ArvoreDosSaberes/Embarcatech-Etapa-2---Projeto-Final/docs/aiot-tool-calling-embarcados/slides/17-conclusao.md

# 🎯 Conclusões e Próximos Passos

## O Que Aprendemos

- **IA é estatística avançada** — Não magia, mas muito útil
- **LLMs + Tool Calling** — Permitem decisões semânticas
- **AIoT** — ESP32 pode ser "inteligente" via nuvem
- **Granite TTM** — Séries temporais com fallback robusto
- **HTTPS no ESP32** — Viável e necessário

## Desafios para Explorar

- **Edge AI** — TinyML, TensorFlow Lite no ESP32
- **Latência** — Decisões locais vs. nuvem
- **Custo** — APIs pagas vs. modelos locais (Ollama)
- **Segurança** — Proteção de tokens e dados

## Recursos

- **Projeto Rack Inteligente**: github.com/...
- **Granite TTM**: ibm.github.io/granite-tsfm
- **ESP-IDF**: docs.espressif.com
- **Ollama**: ollama.ai

> "O melhor momento para começar com IA embarcada foi ontem. O segundo melhor é agora!"
