ArvoreDosSaberes/Embarcatech-Etapa-2---Projeto-Final/docs/aiot-tool-calling-embarcados/slides/index.md

---
title: "AIoT e Tool Calling em Sistemas Embarcados"
subtitle: "Da IA na Nuvem ao ESP32"
authors:
  - "Carlos Delfino Carvalho Pinheiro"
date: "2025"
description: "Apresentação para a comunidade Embarcados sobre AIoT, Tool Calling e integração de LLMs com microcontroladores"
tags:
  - "AIoT"
  - "Tool Calling"
  - "ESP32"
  - "LLM"
  - "Sistemas Embarcados"
---
