ArvoreDosSaberes/Embarcatech-Etapa-2---Projeto-Final/docs/aiot-tool-calling-embarcados/slides/03-ia-vs-ai.md

# 🤔 "Inteligência Artificial" — É Certo Usar Este Nome?

## O Debate Histórico

- **1956**: John McCarthy cunhou o termo "Artificial Intelligence"
- O termo foi **marketing** para obter financiamento de pesquisa
- Críticos argumentam: máquinas não "pensam", apenas **processam padrões**

## O Que Realmente Temos Hoje

| O que chamamos | O que realmente é |
|---|---|
| IA | Estatística avançada + Álgebra linear |
| Aprendizado | Otimização de parâmetros |
| Inteligência | Reconhecimento de padrões |
| Compreensão | Correlação probabilística |

## Por Que Usamos Mesmo Assim?

- **Convenção** — O termo está consolidado
- **Comunicação** — Facilita o diálogo com não-técnicos
- **Evolução** — O significado acompanha a tecnologia

> "Toda tecnologia suficientemente avançada é indistinguível de magia" — Arthur C. Clarke
