ArvoreDosSaberes/Embarcatech-Etapa-2---Projeto-Final/docs/aiot-tool-calling-embarcados/slides/04-genai-llm.md

# 🧠 GenAIs e LLMs — O Que São?

## Generative AI (GenAI)

Sistemas capazes de **gerar conteúdo novo**:
- Texto, imagens, código, áudio, vídeo
- Baseados em padrões aprendidos de dados massivos

## Large Language Models (LLMs)

Modelos de linguagem com **bilhões de parâmetros**:
- **GPT** (OpenAI) — 175B+ parâmetros
- **Granite** (IBM) — Modelos especializados
- **Llama** (Meta) — Open source
- **Gemini** (Google) — Multimodal

## Como Funcionam?

```
[Texto de Entrada] → [Tokenização] → [Embedding] 
         ↓
    [Transformer]
         ↓
[Predição do Próximo Token] → [Decodificação] → [Resposta]
```

## Limitações Importantes

- **Não "entendem"** — Apenas correlacionam padrões
- **Alucinações** — Podem inventar informações
- **Custo computacional** — Exigem muita memória/processamento
