ArvoreDosSaberes/Embarcatech-Etapa-2---Projeto-Final/docs/aiot-tool-calling-embarcados/slides/18-obrigado.md

# 🙏 Obrigado!

## Contato

**Carlos Delfino Carvalho Pinheiro**

- 🧔 Membro honorário da Beard Brotherhood
- 💼 Desenvolvedor Embarcado & IoT
- 🎓 EmbarcaTech TIC-27

---

## Perguntas?

> "A única pergunta boba é aquela que não foi feita!"

---

## Links Úteis

- **OpenAI Docs**: platform.openai.com/docs
- **ESP-IDF HTTPS**: docs.espressif.com/projects/esp-idf
- **IBM Granite**: github.com/ibm-granite
- **Comunidade Embarcados**: embarcados.com.br
