ArvoreDosSaberes/Embarcatech-Etapa-2---Projeto-Final/docs/esquemático/Esquemático Final/3D/3D_1/WhatsApp Image 2024-02-20 at 16.13.23.jpeg

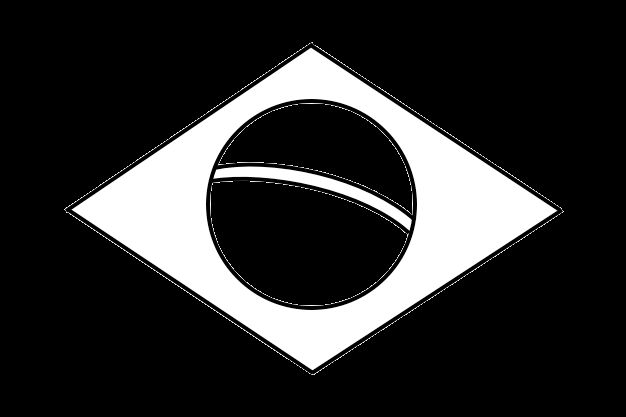
docs/esquemático/Esquemático Final/3D/3D_1/WhatsApp Image 2024-02-20 at 16.13.23.jpeg
