ArvoreDosSaberes/Embarcatech-Etapa-2---Projeto-Final/docs/esquemático/Esquemático Final/3D/3D_1/SMT-microinterruptor moment neo.SLDPRT

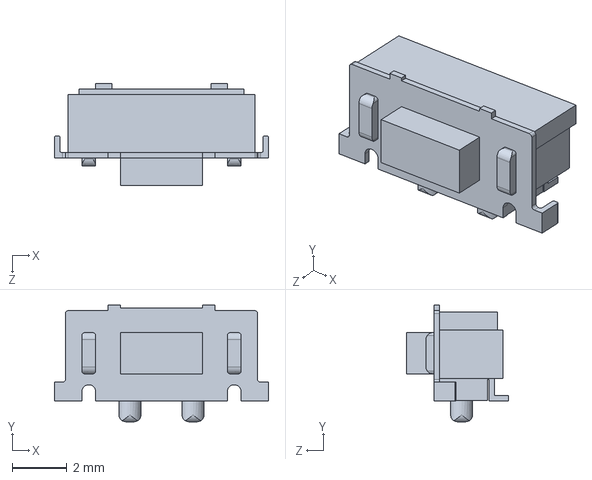
[picture p29: CAD file, 2026-01-02]
docs/esquemático/Esquemático Final/3D/3D_1/SMT-microinterruptor moment neo.SLDPRT
7.80 x 4.25 x 3.70 mm
