ArvoreDosSaberes/Embarcatech-Etapa-2---Projeto-Final/docs/esquemático/Esquemático Final/3D/DS1021_blue_2x01p_100mil_Type5_rev1.0.STEP

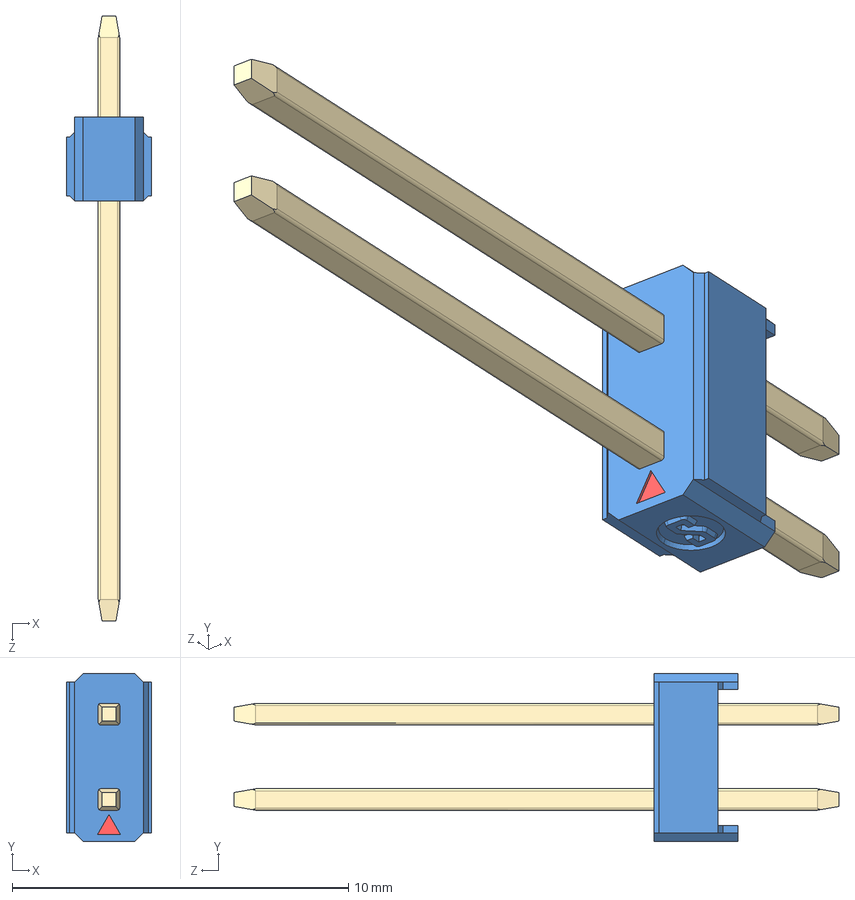
[picture p30: CAD file, 2026-01-02]
docs/esquemático/Esquemático Final/3D/DS1021_blue_2x01p_100mil_Type5_rev1.0.STEP
2.54 x 5.00 x 18.0 mm
