ArvoreDosSaberes/Embarcatech-Etapa-2---Projeto-Final/docs/esquemático/Esquemático Final/3D/3D_1/LED SMD 5050 RGB.stp

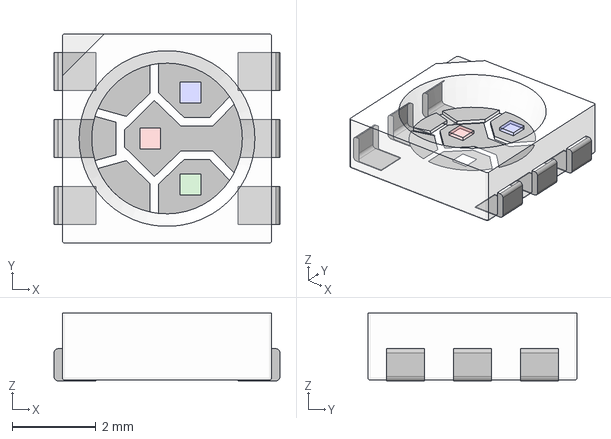
[picture p31: CAD file, 2026-01-02]
docs/esquemático/Esquemático Final/3D/3D_1/LED SMD 5050 RGB.stp
5.40 x 5.00 x 1.62 mm
