ArvoreDosSaberes/Embarcatech-Etapa-2---Projeto-Final/docs/esquemático/Esquemático Final/3D/CONB127P-2R-14W_TH.STEP

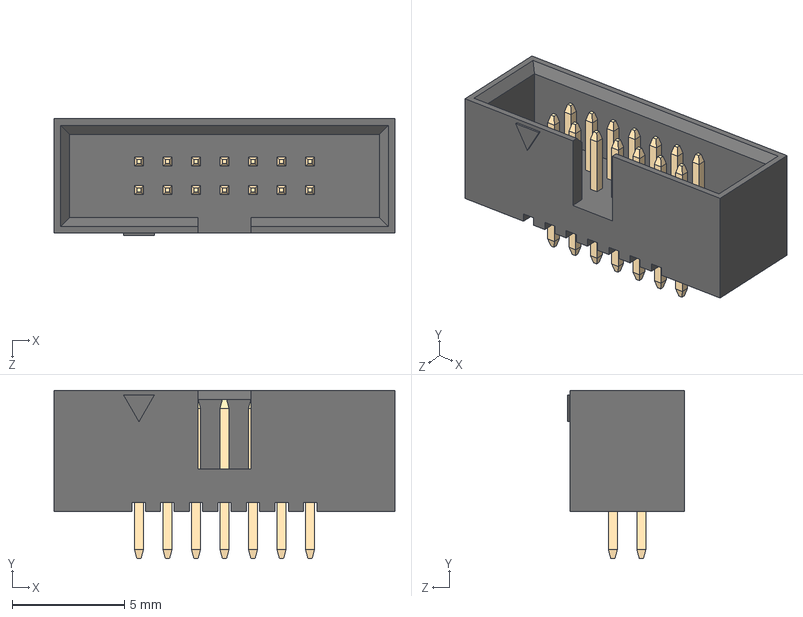
[picture p32: CAD file, 2026-01-02]
docs/esquemático/Esquemático Final/3D/CONB127P-2R-14W_TH.STEP
15.2 x 7.50 x 5.20 mm
