ArvoreDosSaberes/Embarcatech-Etapa-2---Projeto-Final/docs/esquemático/Esquemático Final/3D/3D_1/SOP-8.STEP

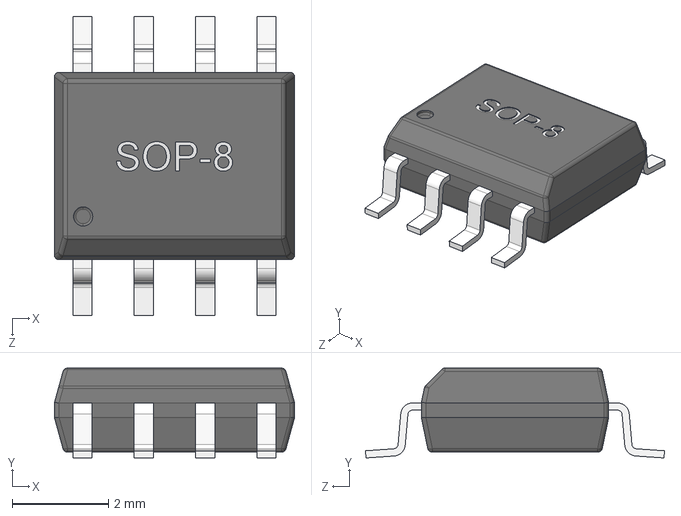
[picture p33: CAD file, 2026-01-02]
docs/esquemático/Esquemático Final/3D/3D_1/SOP-8.STEP
5.00 x 1.87 x 6.22 mm
