ArvoreDosSaberes/Embarcatech-Etapa-2---Projeto-Final/docs/esquemático/Esquemático Final/3D/TL800-02.STEP

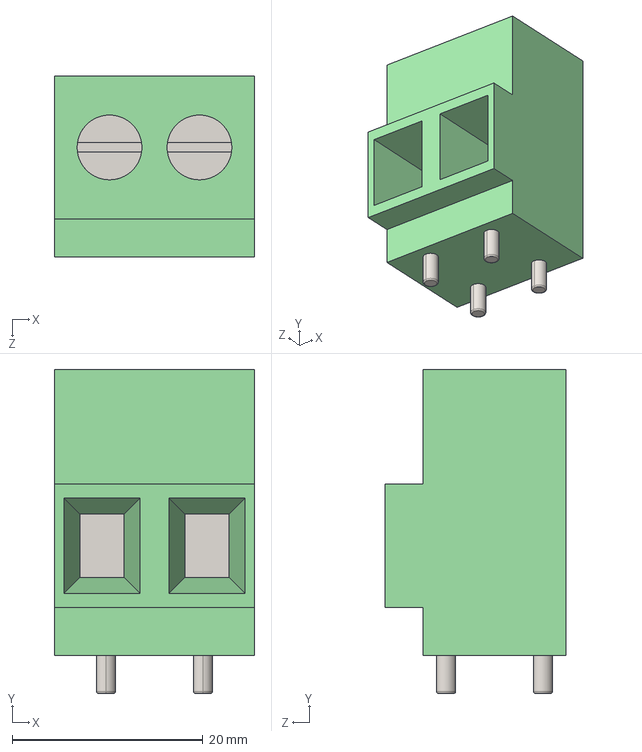
[picture p34: CAD file, 2026-01-02]
docs/esquemático/Esquemático Final/3D/TL800-02.STEP
21.0 x 34.0 x 19.0 mm
