ArvoreDosSaberes/Embarcatech-Etapa-2---Projeto-Final/docs/esquemático/Esquemático Final/3D/12mm Push Button with Cap.STEP

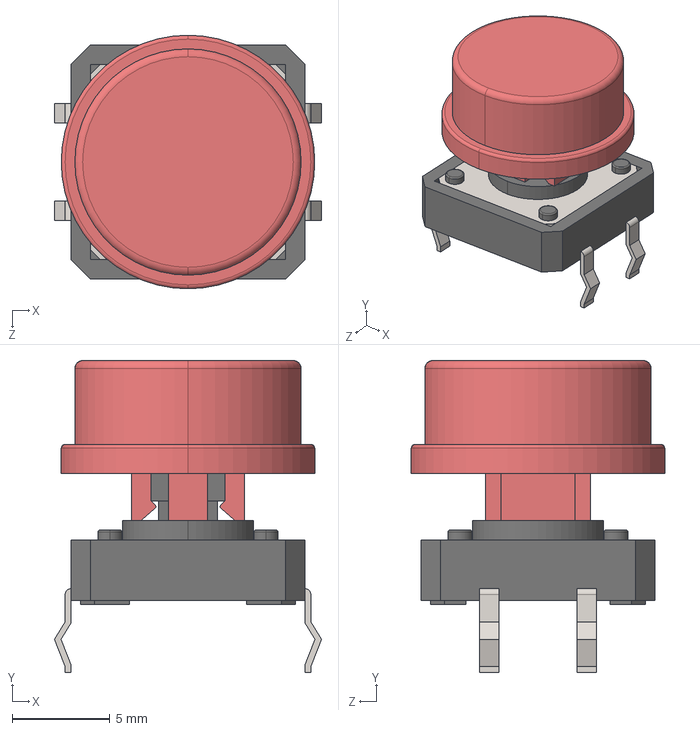
[picture p35: CAD file, 2026-01-02]
docs/esquemático/Esquemático Final/3D/12mm Push Button with Cap.STEP
13.7 x 16.0 x 13.0 mm
12mm Push Button
12mm Push Button Cap
