ArvoreDosSaberes/Embarcatech-Etapa-2---Projeto-Final/docs/esquemático/Esquemático Final/3D/3D_1/SC70-5.step

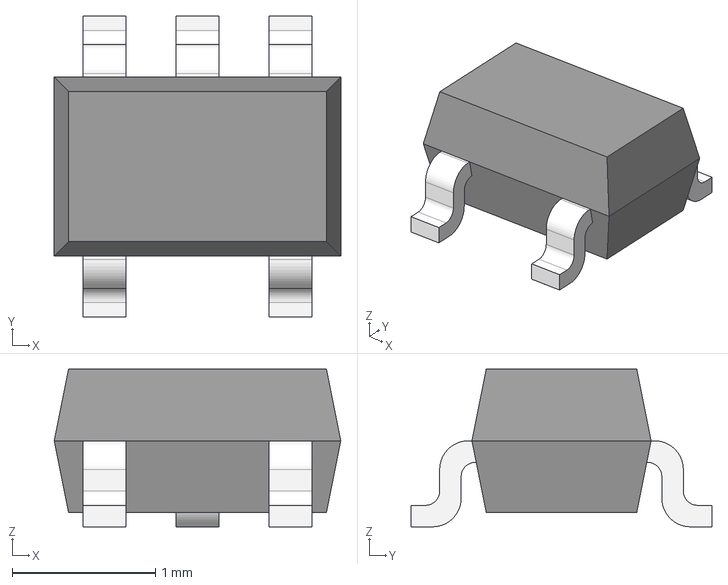
[picture p36: CAD file, 2026-01-02]
docs/esquemático/Esquemático Final/3D/3D_1/SC70-5.step
2.00 x 2.10 x 1.10 mm
