ArvoreDosSaberes/Embarcatech-Etapa-2---Projeto-Final/docs/esquemático/Esquemático Final/3D/3D_1/PLS-1X5.step

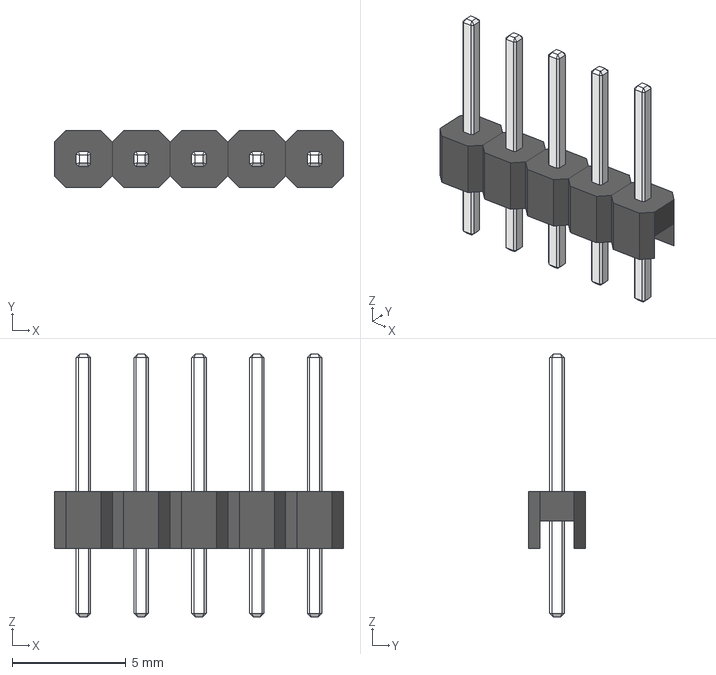
[picture p37: CAD file, 2026-01-02]
docs/esquemático/Esquemático Final/3D/3D_1/PLS-1X5.step
12.7 x 2.50 x 11.5 mm
