ArvoreDosSaberes/Embarcatech-Etapa-2---Projeto-Final/docs/esquemático/Esquemático Final/3D/LED - SMD RGB (WS2812).sldprt

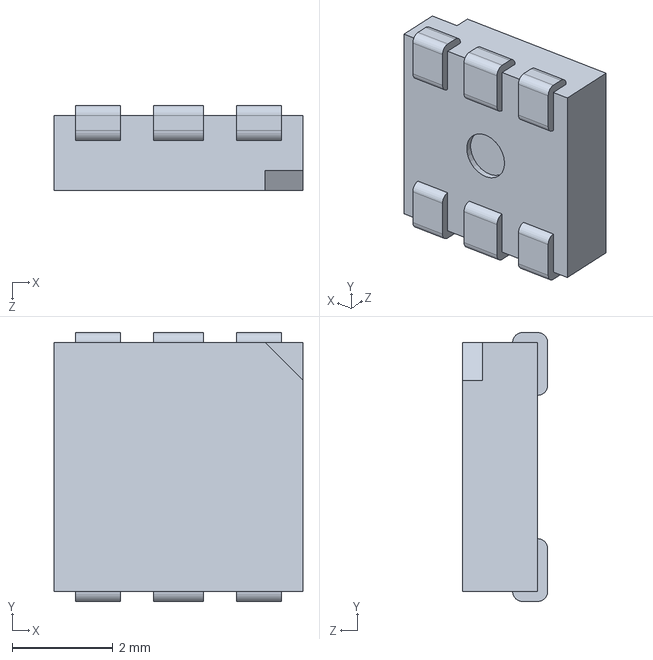
[picture p38: CAD file, 2026-01-02]
docs/esquemático/Esquemático Final/3D/LED - SMD RGB (WS2812).sldprt
4.95 x 5.35 x 1.70 mm
