ArvoreDosSaberes/Embarcatech-Etapa-2---Projeto-Final/docs/esquemático/Esquemático Final/3D/3D_1/SOT-23.step

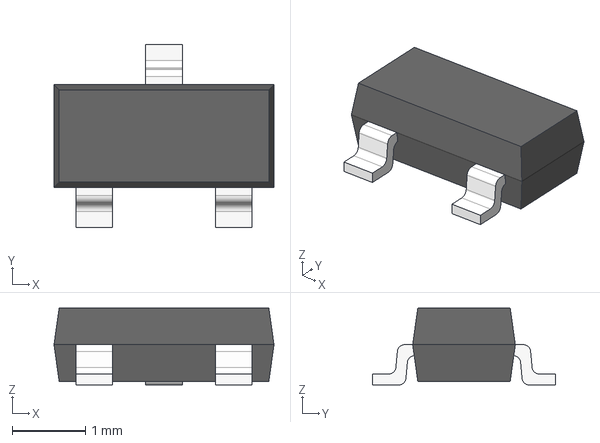
[picture p39: CAD file, 2026-01-02]
docs/esquemático/Esquemático Final/3D/3D_1/SOT-23.step
3.00 x 2.50 x 1.05 mm
