ArvoreDosSaberes/Embarcatech-Etapa-2---Projeto-Final/docs/esquemático/Esquemático Final/3D/3D_1/HwIT-Without-Slogan-800x600.dxf

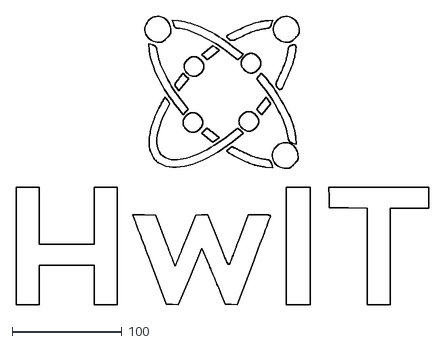
[picture p40: CAD file, 2026-01-02]
docs/esquemático/Esquemático Final/3D/3D_1/HwIT-Without-Slogan-800x600.dxf
376.0 x 262.9
