ArvoreDosSaberes/Embarcatech-Etapa-2---Projeto-Final/docs/esquemático/Esquemático Final/3D/C_0805.STEP

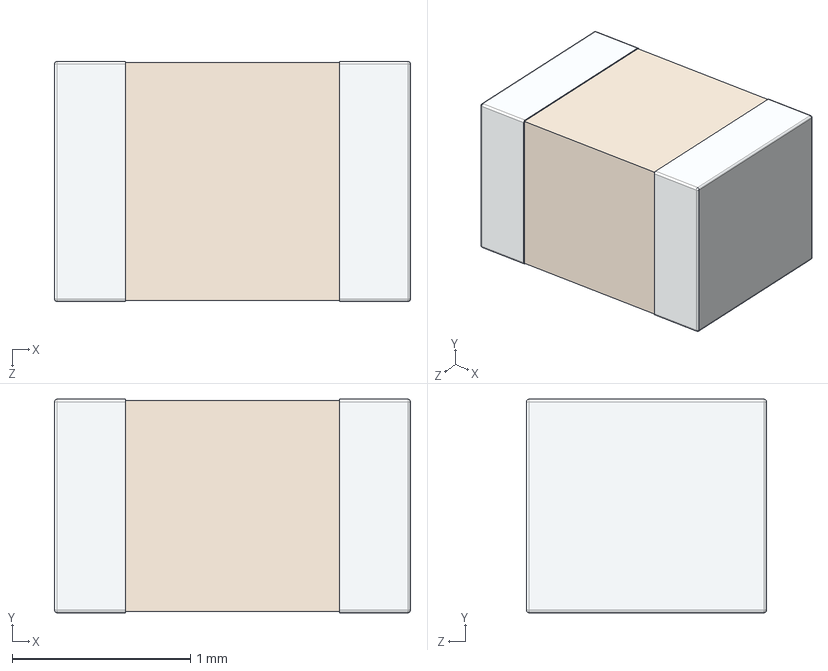
[picture p41: CAD file, 2026-01-02]
docs/esquemático/Esquemático Final/3D/C_0805.STEP
2.00 x 1.20 x 1.35 mm
