ArvoreDosSaberes/Embarcatech-Etapa-2---Projeto-Final/docs/esquemático/Esquemático Final/3D/3D_1/AB2_HDR_M07-2V-S-TE_WINGS3D.stl

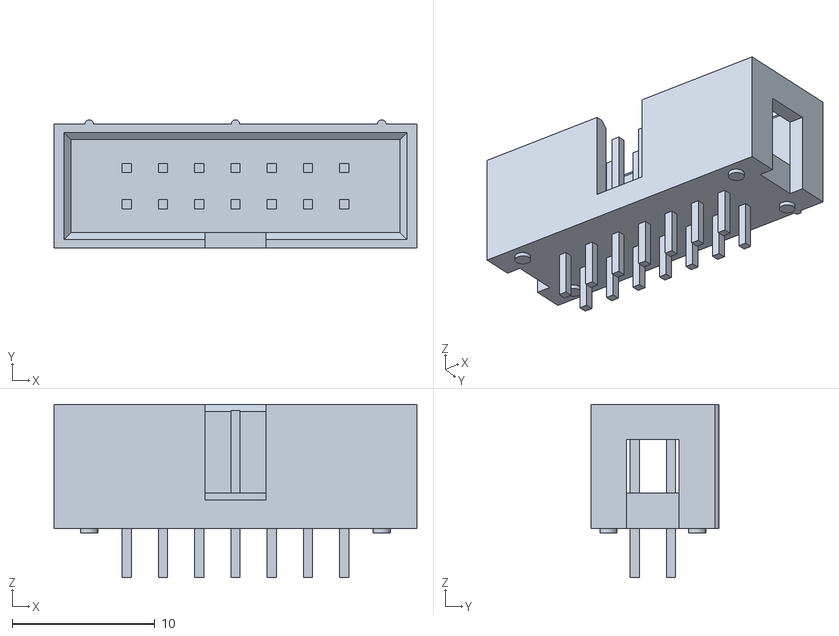
[picture p42: CAD file, 2026-01-02]
docs/esquemático/Esquemático Final/3D/3D_1/AB2_HDR_M07-2V-S-TE_WINGS3D.stl
25.4 x 9.00 x 12.1
