ArvoreDosSaberes/Embarcatech-Etapa-2---Projeto-Final/docs/esquemático/Esquemático Final/3D/Resistor_0603_Ohm.step

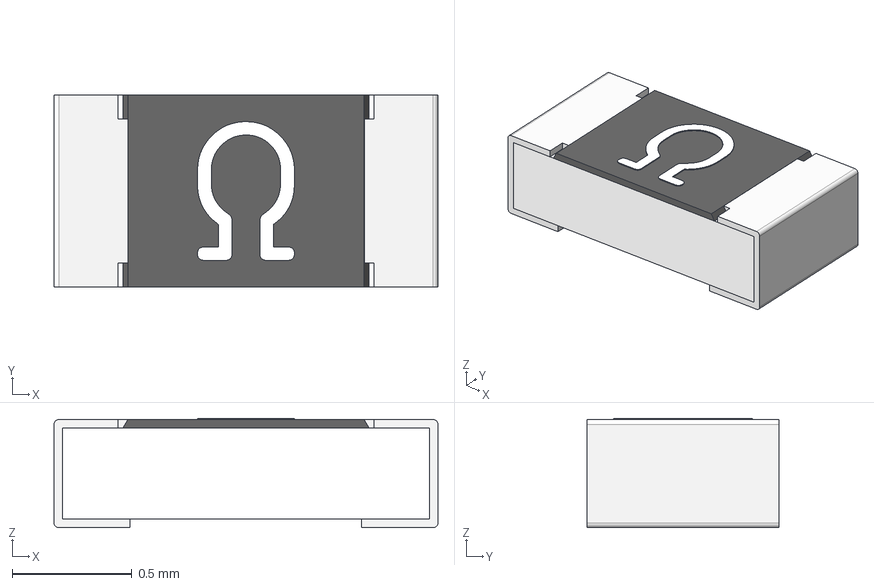
[picture p43: CAD file, 2026-01-02]
docs/esquemático/Esquemático Final/3D/Resistor_0603_Ohm.step
1.60 x 0.8 x 0.455 mm
Pin1Body
Pin2Body
CeramicBody
CoatingBody
TextBody
