ArvoreDosSaberes/Embarcatech-Etapa-2---Projeto-Final/docs/esquemático/Esquemático Final/3D/3D_1/EVM-3E.STEP

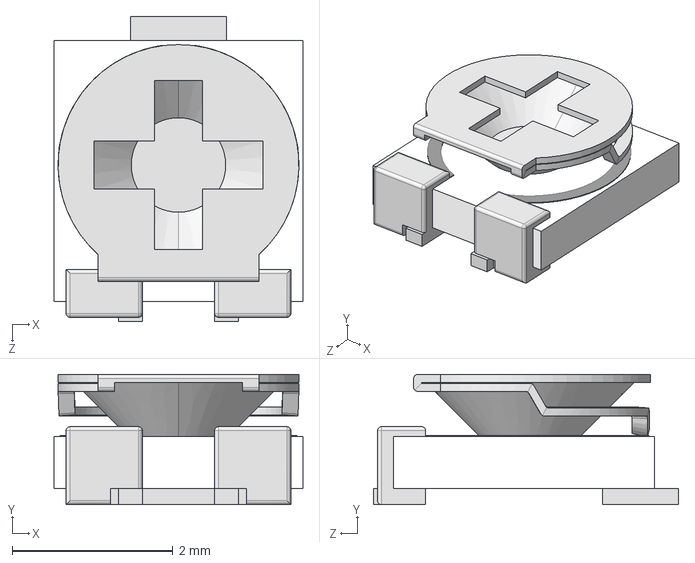
[picture p44: CAD file, 2026-01-02]
docs/esquemático/Esquemático Final/3D/3D_1/EVM-3E.STEP
3.10 x 1.62 x 3.80 mm
