ArvoreDosSaberes/Embarcatech-Etapa-2---Projeto-Final/docs/esquemático/Esquemático Final/3D/3D_1/C_0603.STEP

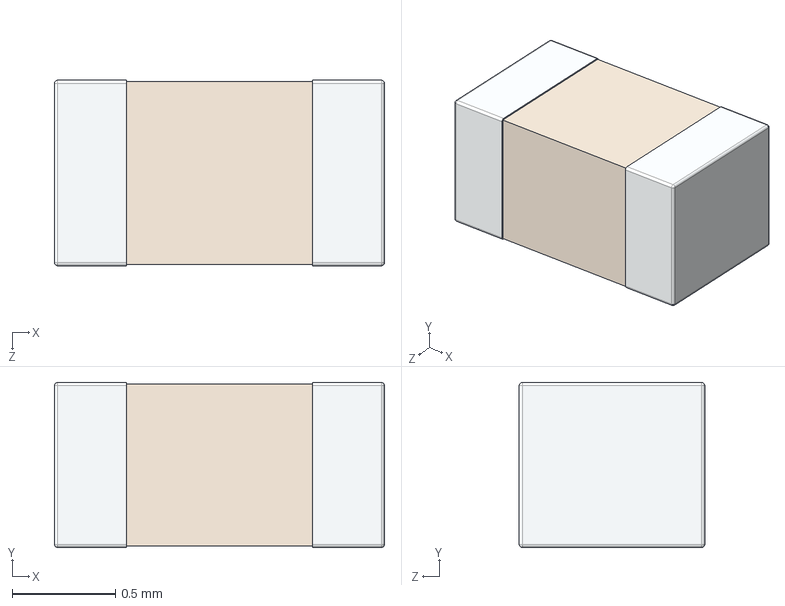
[picture p45: CAD file, 2026-01-02]
docs/esquemático/Esquemático Final/3D/3D_1/C_0603.STEP
1.60 x 0.8 x 0.9 mm
