ArvoreDosSaberes/Embarcatech-Etapa-2---Projeto-Final/docs/esquemático/Esquemático Final/3D/smd Led 5050 v3.step

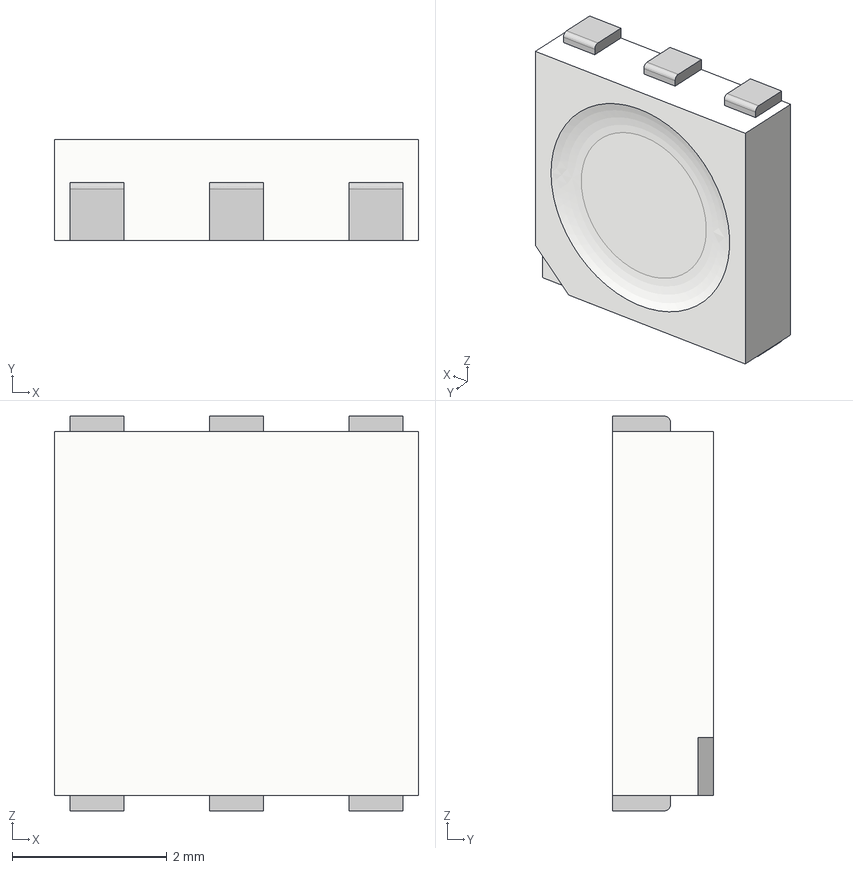
[picture p46: CAD file, 2026-01-02]
docs/esquemático/Esquemático Final/3D/smd Led 5050 v3.step
4.70 x 1.30 x 5.10 mm
