ArvoreDosSaberes/Embarcatech-Etapa-2---Projeto-Final/docs/esquemático/Esquemático Final/3D/3D_1/pin header pitch v4.step

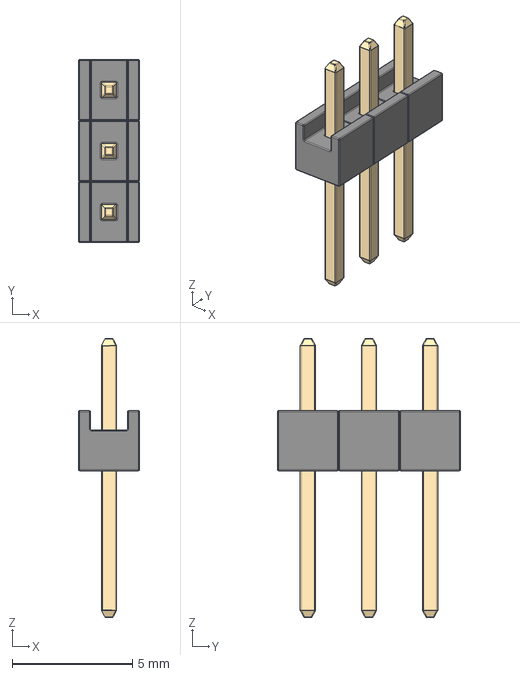
[picture p47: CAD file, 2026-01-02]
docs/esquemático/Esquemático Final/3D/3D_1/pin header pitch v4.step
2.54 x 7.62 x 11.6 mm
