ArvoreDosSaberes/Embarcatech-Etapa-2---Projeto-Final/docs/esquemático/Esquemático Final/3D/JST XH 4 B4B-XH-A.STEP

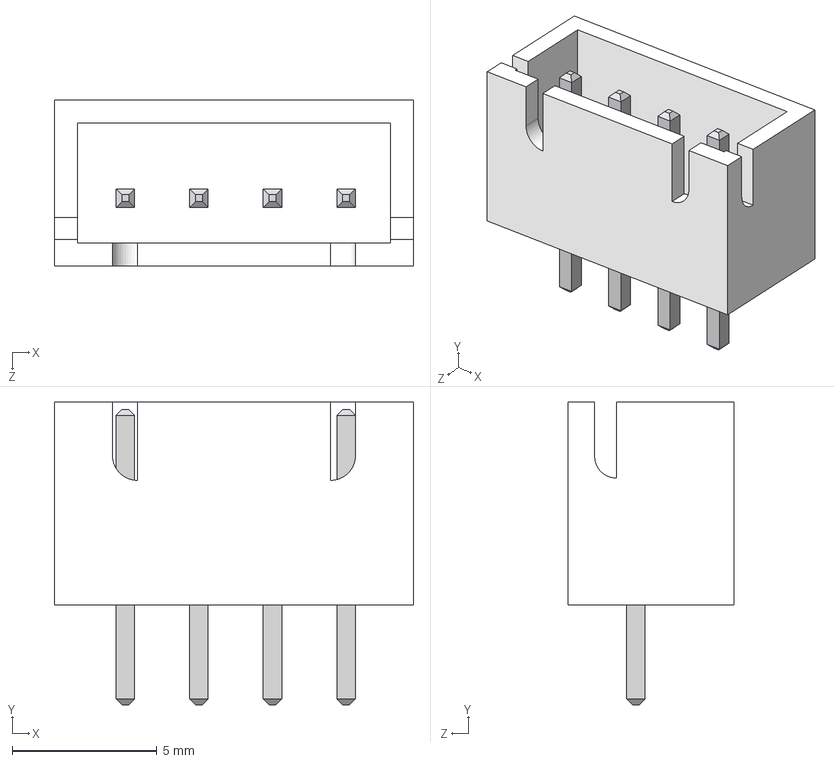
[picture p48: CAD file, 2026-01-02]
docs/esquemático/Esquemático Final/3D/JST XH 4 B4B-XH-A.STEP
12.4 x 10.5 x 5.75 mm
