ArvoreDosSaberes/Embarcatech-Etapa-2---Projeto-Final/docs/esquemático/Esquemático Final/3D/Pushbutton (TC-1101DE-B-D_C561494) Code _ B.step

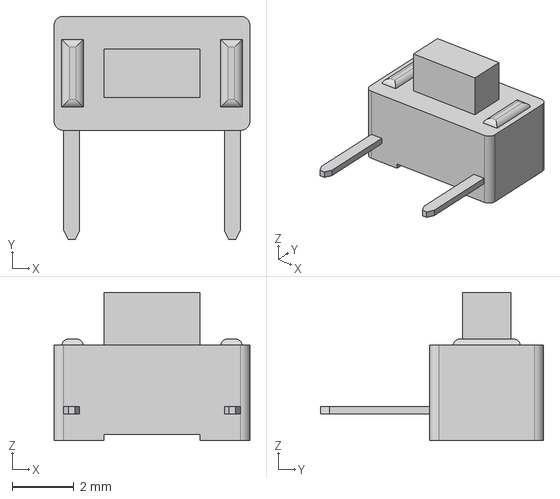
[picture p49: CAD file, 2026-01-02]
docs/esquemático/Esquemático Final/3D/Pushbutton (TC-1101DE-B-D_C561494) Code _ B.step
6.34 x 7.23 x 4.80 mm
