ArvoreDosSaberes/Embarcatech-Etapa-2---Projeto-Final/docs/esquemático/Esquemático Final/3D/C_0402.STEP

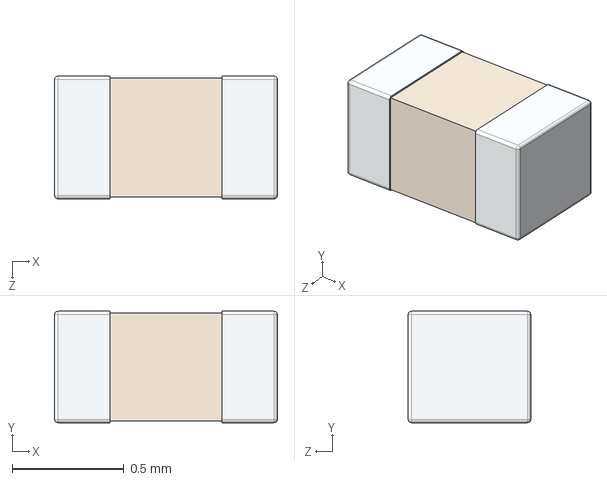
[picture p50: CAD file, 2026-01-02]
docs/esquemático/Esquemático Final/3D/C_0402.STEP
1.00 x 0.5 x 0.55 mm
