ArvoreDosSaberes/Embarcatech-Etapa-2---Projeto-Final/docs/esquemático/Esquemático Final/3D/3D_1/AnyConv.com__HwIT Without Slogan 2400x1800.dxf

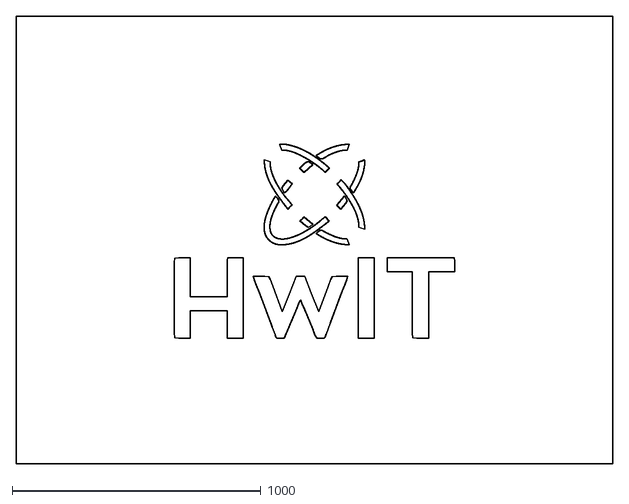
[picture p51: CAD file, 2026-01-02]
docs/esquemático/Esquemático Final/3D/3D_1/AnyConv.com__HwIT Without Slogan 2400x1800.dxf
2400.0 x 1800.0
