ArvoreDosSaberes/Embarcatech-Etapa-2---Projeto-Final/docs/esquemático/Esquemático Final/3D/MAX4466 Mic Amp.STEP

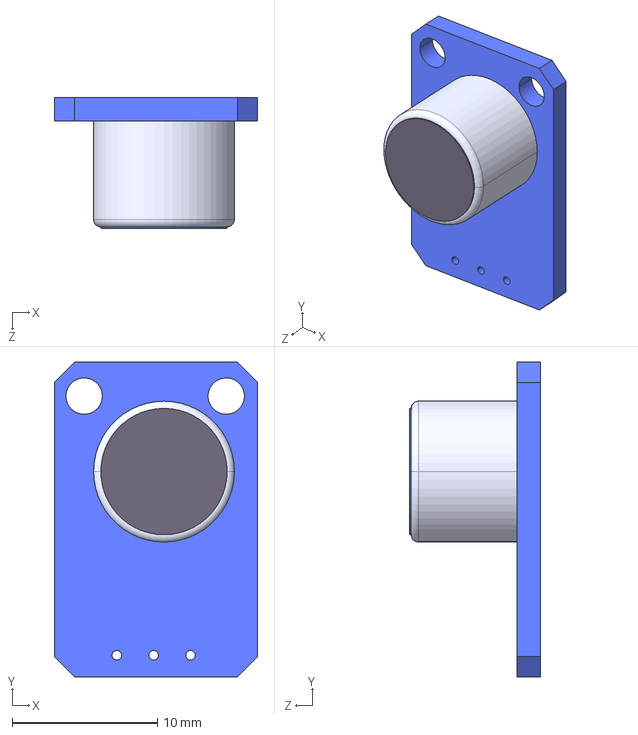
[picture p52: CAD file, 2026-01-02]
docs/esquemático/Esquemático Final/3D/MAX4466 Mic Amp.STEP
14.0 x 21.7 x 9.00 mm
