ArvoreDosSaberes/Embarcatech-Etapa-2---Projeto-Final/docs/esquemático/Esquemático Final/3D/3D_1/PSM8050 Series SMD Molding inductor.STEP

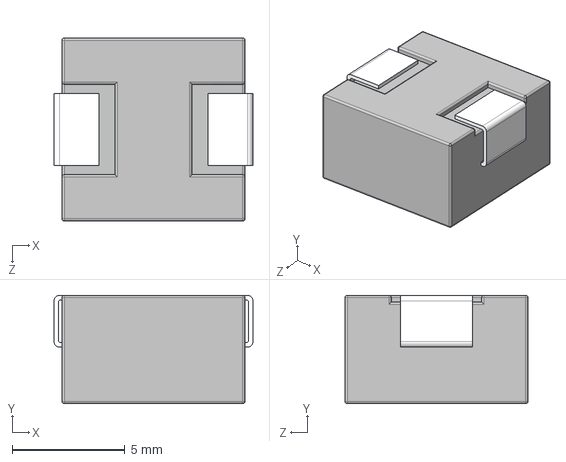
[picture p53: CAD file, 2026-01-02]
docs/esquemático/Esquemático Final/3D/3D_1/PSM8050 Series SMD Molding inductor.STEP
8.81 x 4.80 x 8.10 mm
