ArvoreDosSaberes/Embarcatech-Etapa-2---Projeto-Final/docs/esquemático/Esquemático Final/3D/SparkFun Deluxe Thumbstick with Breakout Board and Knob.step

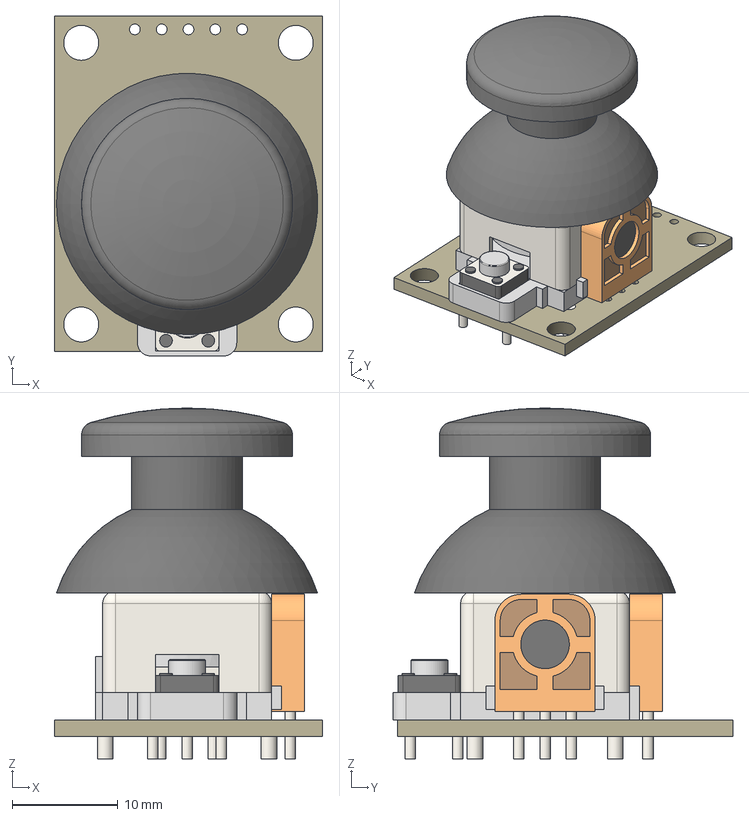
[picture p54: CAD file, 2026-01-02]
docs/esquemático/Esquemático Final/3D/SparkFun Deluxe Thumbstick with Breakout Board and Knob.step
25.4 x 32.2 x 33.2 mm
Board
SFE-LOGO-FLAME
SFE-NEW-WEBLOGO
Thumbstick
