ArvoreDosSaberes/Embarcatech-Etapa-2---Projeto-Final/docs/esquemático/Esquemático Final/3D/3D_1/ALU_CAP_1uF_50V.STEP

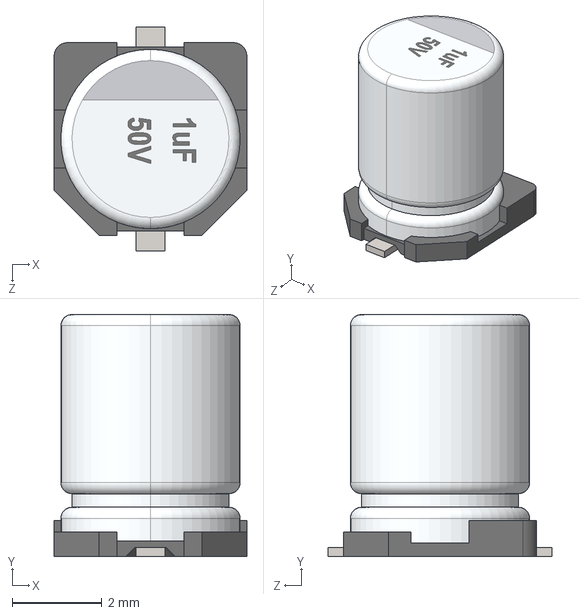
[picture p55: CAD file, 2026-01-02]
docs/esquemático/Esquemático Final/3D/3D_1/ALU_CAP_1uF_50V.STEP
4.30 x 5.40 x 5.00 mm
