ArvoreDosSaberes/Embarcatech-Etapa-2---Projeto-Final/docs/esquemático/Esquemático Final/3D/TC33X-2-104E.STEP

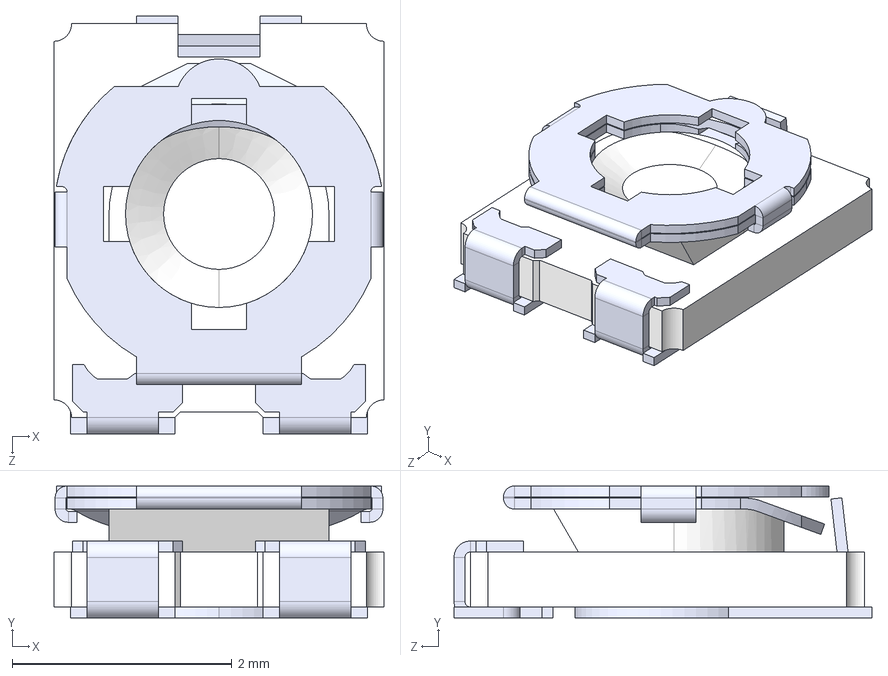
[picture p56: CAD file, 2026-01-02]
docs/esquemático/Esquemático Final/3D/TC33X-2-104E.STEP
3.00 x 1.20 x 3.80 mm
