ArvoreDosSaberes/Embarcatech-Etapa-2---Projeto-Final/docs/esquemático/Esquemático Final/3D/3D_1/HwIT-Without-Slogan-2400x1800.dxf

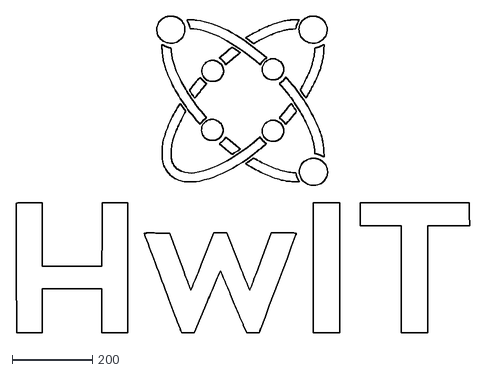
[picture p57: CAD file, 2026-01-02]
docs/esquemático/Esquemático Final/3D/3D_1/HwIT-Without-Slogan-2400x1800.dxf
1127.9 x 788.9
