ArvoreDosSaberes/Embarcatech-Etapa-2---Projeto-Final/docs/esquemático/Esquemático Final/3D/3D_1/KLS3-MT-09.step

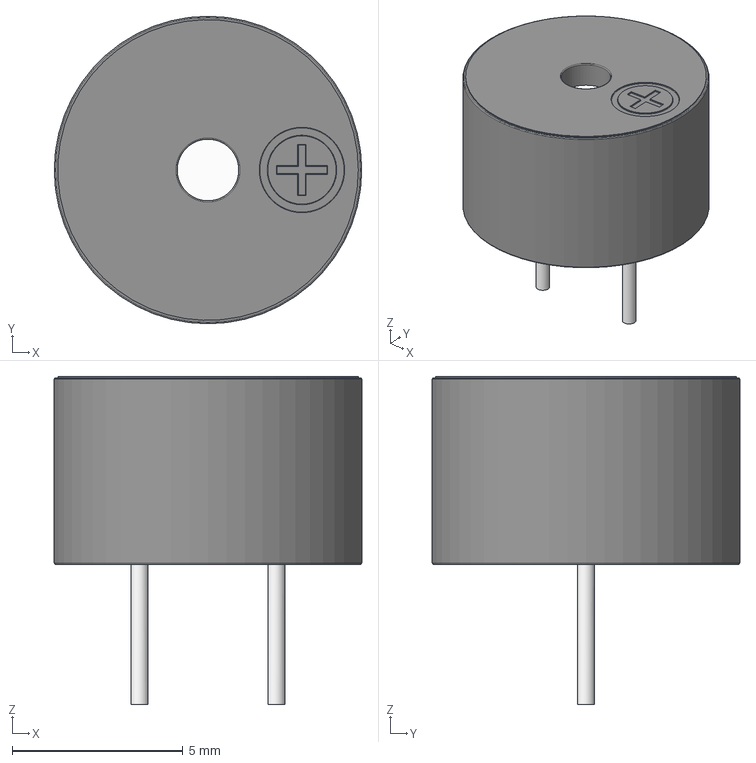
[picture p58: CAD file, 2026-01-02]
docs/esquemático/Esquemático Final/3D/3D_1/KLS3-MT-09.step
9.00 x 9.00 x 9.60 mm
