ArvoreDosSaberes/Embarcatech-Etapa-2---Projeto-Final/docs/esquemático/Esquemático Final/3D/KF128-2.54-2P.step

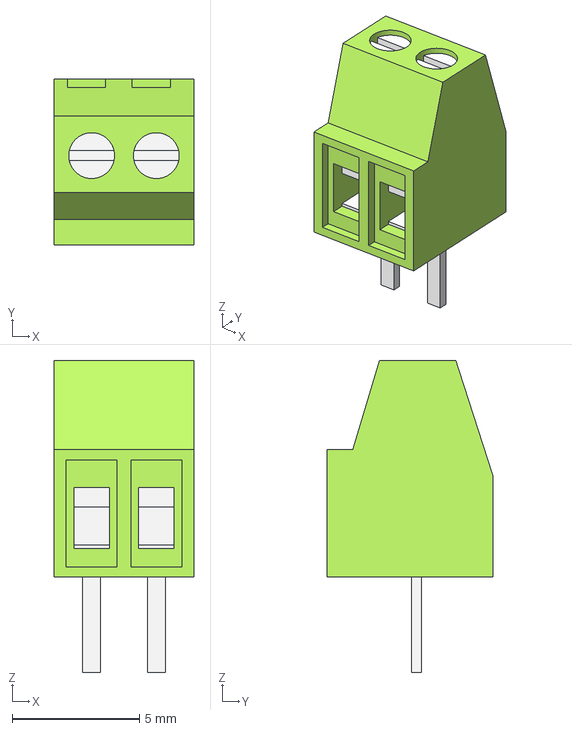
[picture p59: CAD file, 2026-01-02]
docs/esquemático/Esquemático Final/3D/KF128-2.54-2P.step
5.48 x 6.50 x 12.3 mm
Housing
PlasticBody
