ArvoreDosSaberes/Embarcatech-Etapa-2---Projeto-Final/docs/esquemático/Esquemático Final/3D/3D_1/D4_H5.4.step

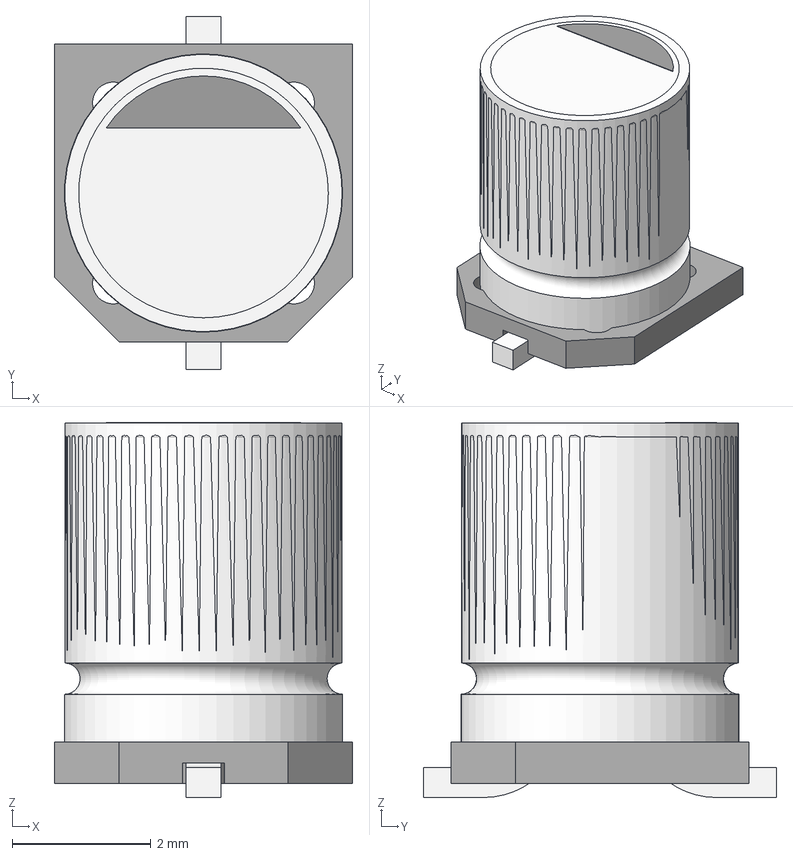
[picture p60: CAD file, 2026-01-02]
docs/esquemático/Esquemático Final/3D/3D_1/D4_H5.4.step
4.30 x 5.10 x 5.41 mm
Socle
Pins
Mark
Pins001
