ArvoreDosSaberes/Embarcatech-Etapa-2---Projeto-Final/docs/esquemático/Esquemático Final/3D/3D_1/APA102C.STEP

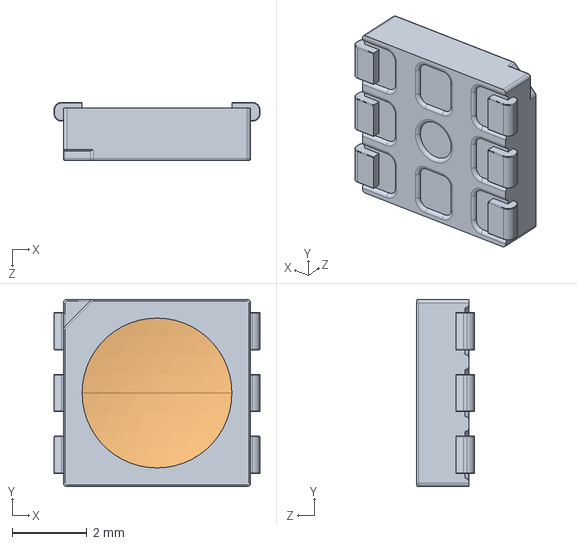
[picture p61: CAD file, 2026-01-02]
docs/esquemático/Esquemático Final/3D/3D_1/APA102C.STEP
5.50 x 5.00 x 1.55 mm
