ArvoreDosSaberes/Embarcatech-Etapa-2---Projeto-Final/docs/esquemático/Esquemático Final/3D/0603 Chip SMD LED (1.6x0.8mm).STEP

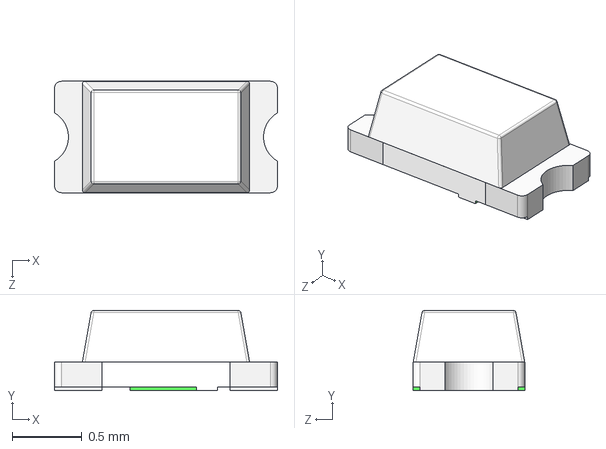
[picture p62: CAD file, 2026-01-02]
docs/esquemático/Esquemático Final/3D/0603 Chip SMD LED (1.6x0.8mm).STEP
1.60 x 0.575 x 0.8 mm
