ArvoreDosSaberes/Embarcatech-Etapa-2---Projeto-Final/docs/esquemático/Esquemático Final/3D/3D_1/9x12 Buzzer.step

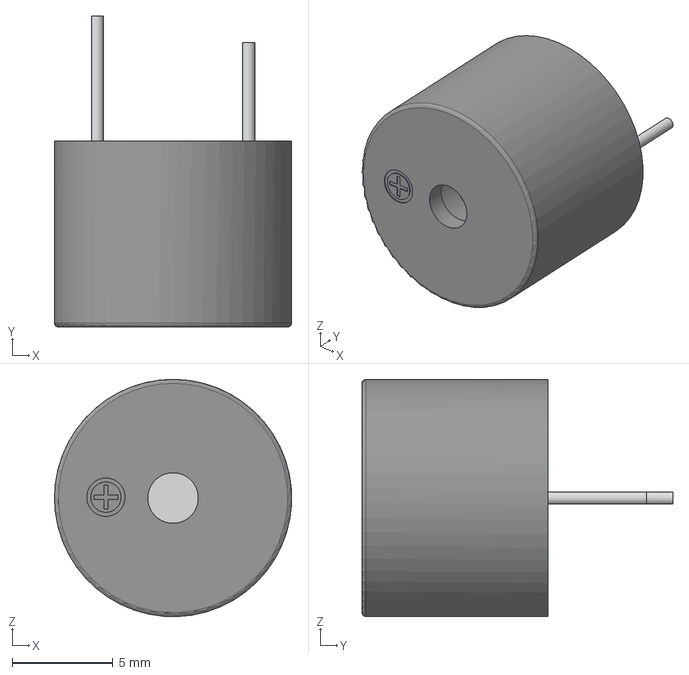
[picture p63: CAD file, 2026-01-02]
docs/esquemático/Esquemático Final/3D/3D_1/9x12 Buzzer.step
11.7 x 15.4 x 11.7 mm
