ArvoreDosSaberes/Embarcatech-Etapa-2---Projeto-Final/docs/esquemático/Esquemático Final/3D/ts-1010gs-x.stp

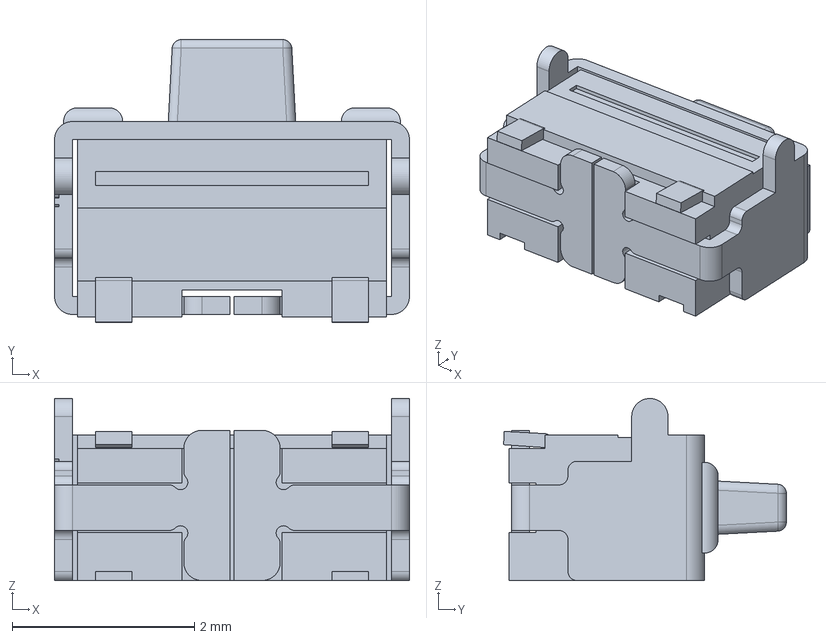
[picture p64: CAD file, 2026-01-02]
docs/esquemático/Esquemático Final/3D/ts-1010gs-x.stp
3.90 x 3.11 x 2.00 mm
