ArvoreDosSaberes/Embarcatech-Etapa-2---Projeto-Final/docs/esquemático/Esquemático Final/3D/3D_1/mypushbutton.stp

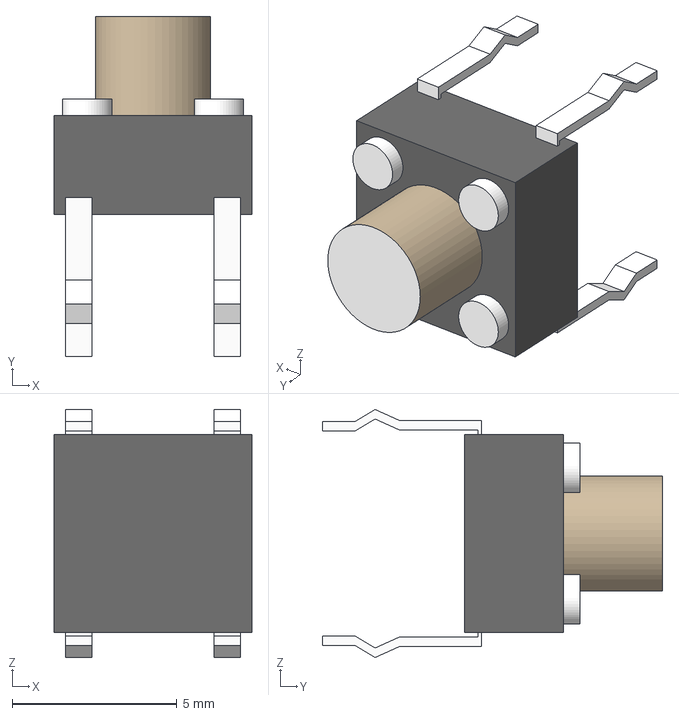
[picture p65: CAD file, 2026-01-02]
docs/esquemático/Esquemático Final/3D/3D_1/mypushbutton.stp
6.00 x 10.3 x 7.52 mm
