ArvoreDosSaberes/Embarcatech-Etapa-2---Projeto-Final/docs/esquemático/Esquemático Final/3D/PushButton.STEP

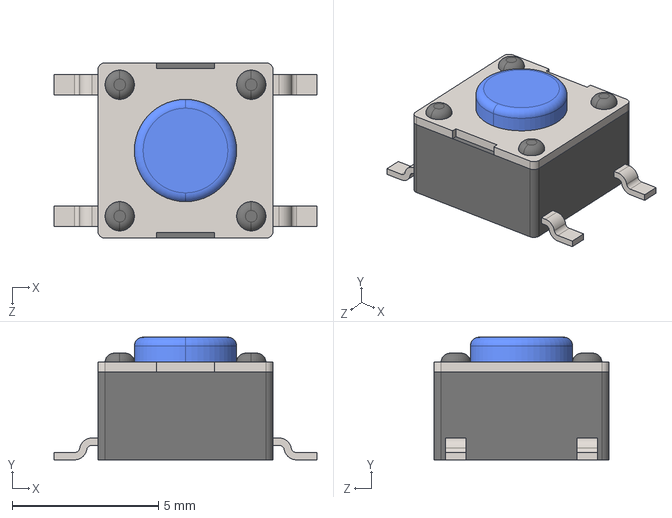
[picture p66: CAD file, 2026-01-02]
docs/esquemático/Esquemático Final/3D/PushButton.STEP
9.00 x 4.20 x 6.00 mm
