ArvoreDosSaberes/Embarcatech-Etapa-2---Projeto-Final/docs/esquemático/Esquemático Final/3D/EMCON_AK700_2P_V.STEP

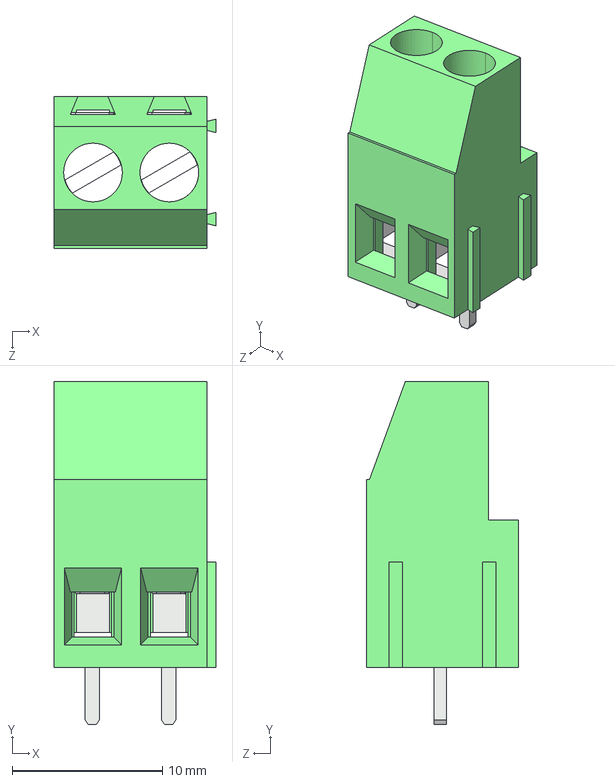
[picture p67: CAD file, 2026-01-02]
docs/esquemático/Esquemático Final/3D/EMCON_AK700_2P_V.STEP
10.8 x 22.8 x 10.1 mm
